YangPiCui/ErgonomicVerticalKeyboard/Versions/EVK_v0.1.0/CaseDesign/README.md

# Case Design 
I have previously outlined the [design process](https://github.com/YangPiCui/ErgonomicVerticalKeyboard/tree/master/EVKVersions/EVK_v0.0/Case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) with Siemens NX in EVK v0.0. Since then, I have found that
* A circular keywell works better. Our hands, not just our fingers, should also move while typing.
* A thumbrest is unnecessary. A free thumb is a more comfortable thumb.  
Below summary is based on EVK v0.1.2  

### Set the Tolerances
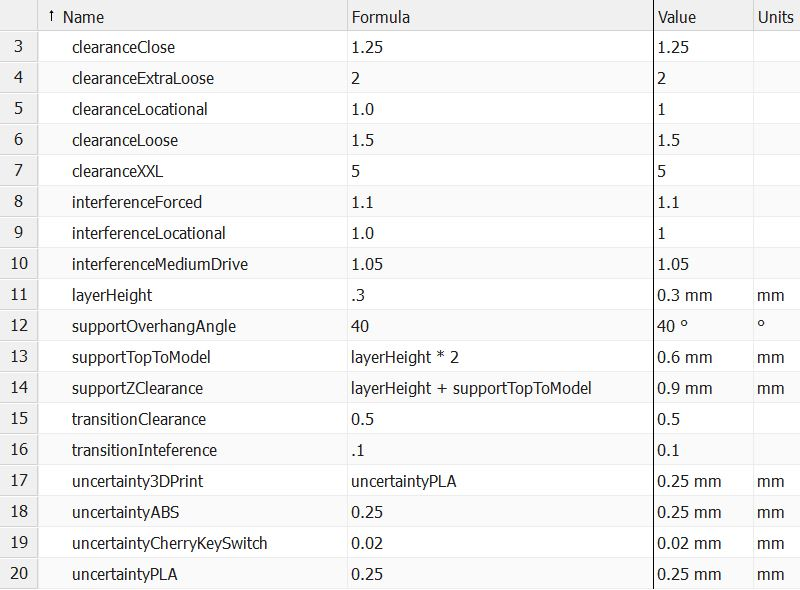
[picture p37: Versions/EVK_v0.1.0/CaseDesign/ToleranceAndClearance0.jpg]


### Design the Keycaps
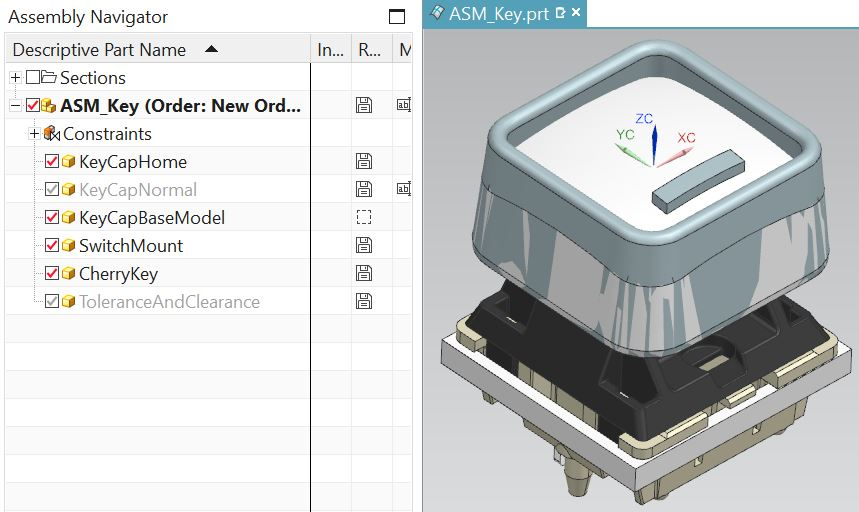
[picture p38: Versions/EVK_v0.1.0/CaseDesign/ASM_Key0.jpg]


### Oriente the Keys for the Middle Finger
ASM_MASTER_MidFingerColumn.prt  
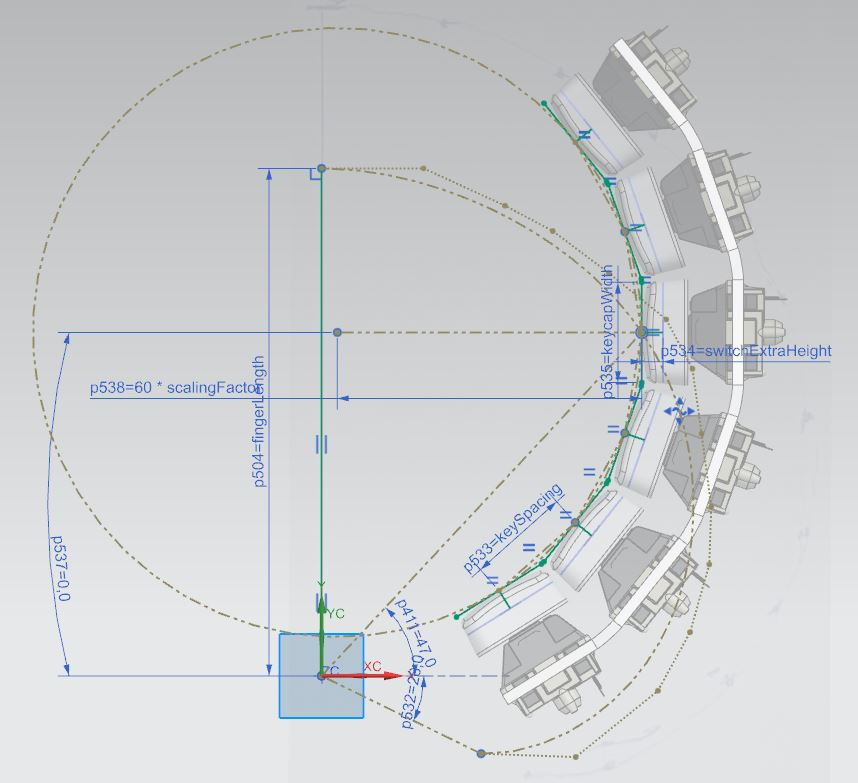
[picture p39: Versions/EVK_v0.1.0/CaseDesign/ASM_MASTER_MidFingerColumn0.jpg]
  

### Position the KeyMounts
Use the Family Part feature to generate keys for the other long fingers.   
Oriente the thumb keys with respect to the middle finger.  
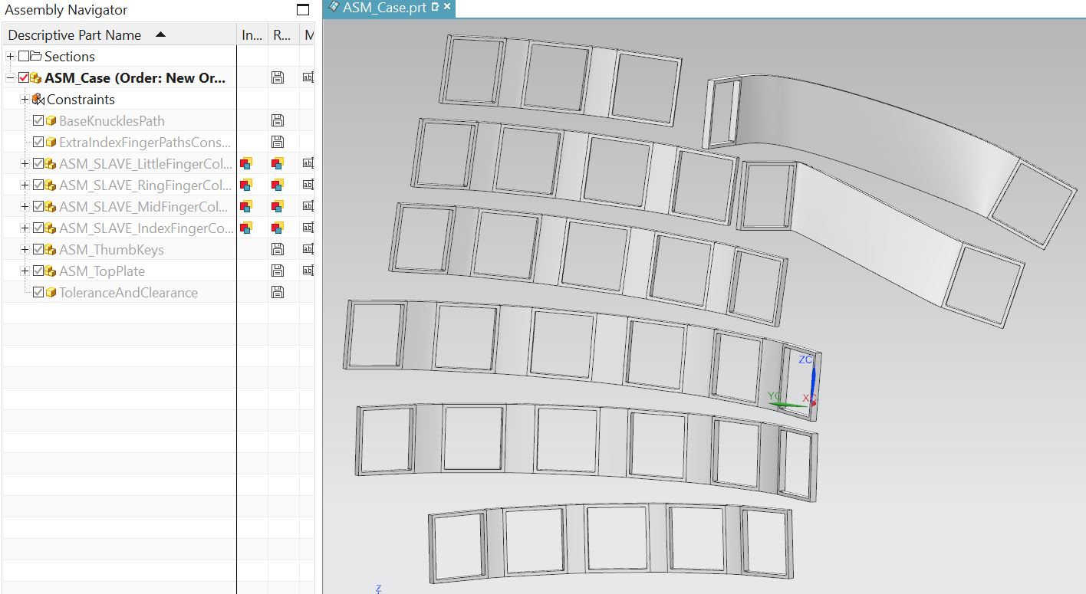
[picture p40: Versions/EVK_v0.1.0/CaseDesign/ASM_Case0.jpg]
  

### Connect the KeyMounts
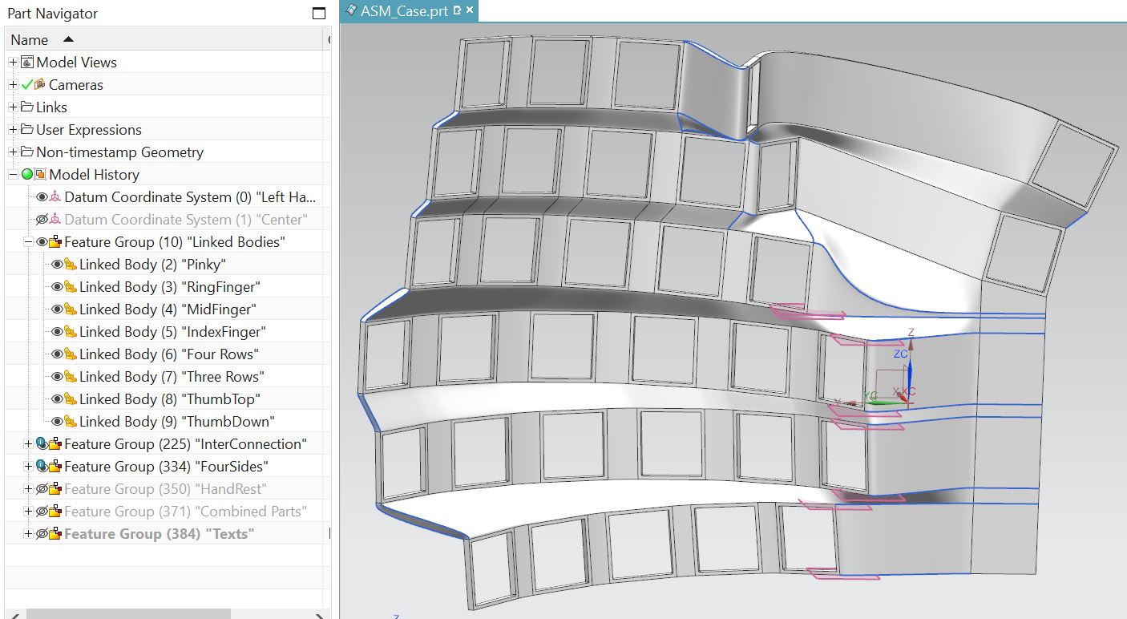
[picture p41: Versions/EVK_v0.1.0/CaseDesign/ASM_Case1.jpg]
  

### Draw the Walls
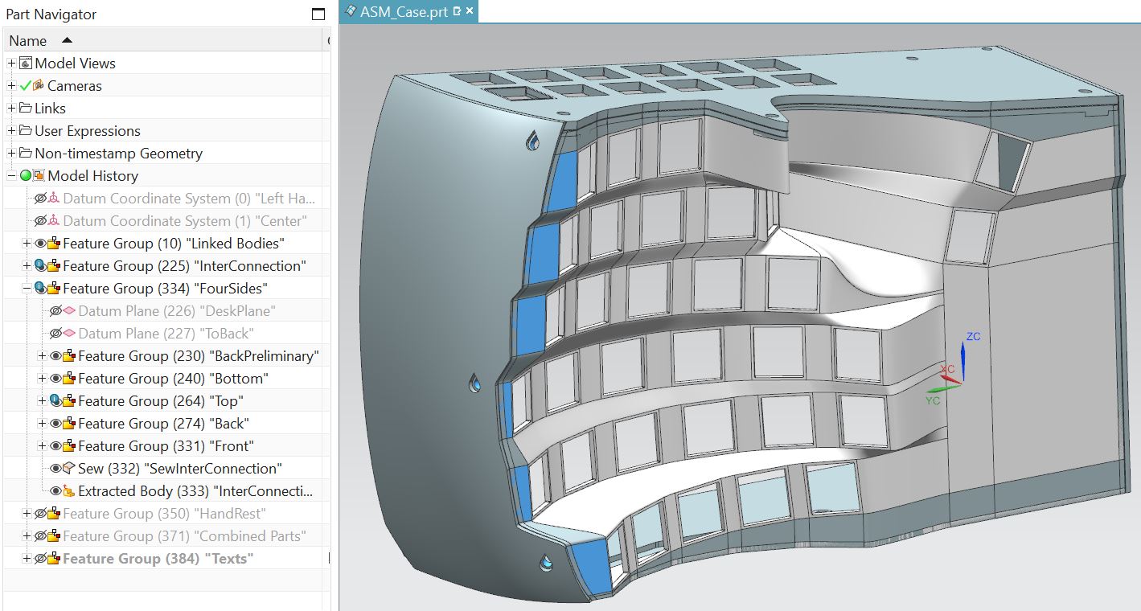
[picture p42: Versions/EVK_v0.1.0/CaseDesign/ASM_Case2.jpg]
 

### Add HandRest and Sponsor Message
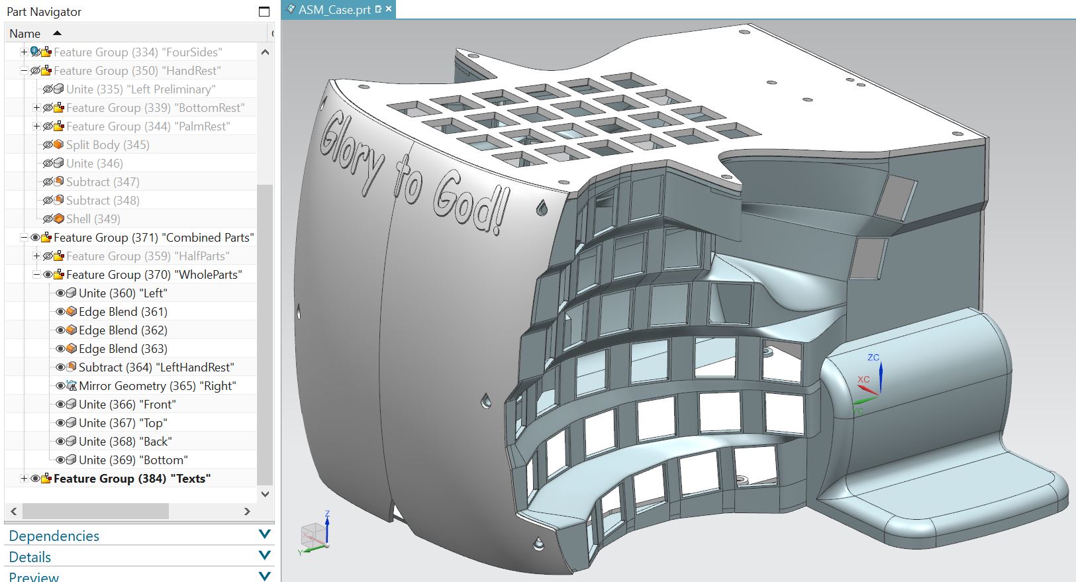
[picture p43: Versions/EVK_v0.1.0/CaseDesign/ASM_Case3.jpg]
 

###### [ODC Open Database License v1.0](https://choosealicense.com/appendix/)  (free but no patent or commercial use)
